C-Falconer/Inscryption/Code/Python/Resources/Images/Background3.jpg

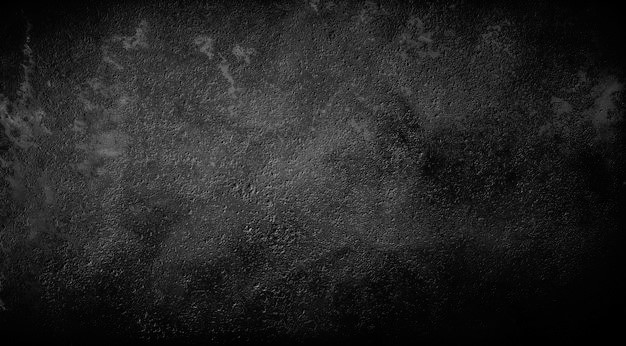
Code/Python/Resources/Images/Background3.jpg
