C-Falconer/Inscryption/Code/Python/Resources/Images/Backgroundv2.3.jpg

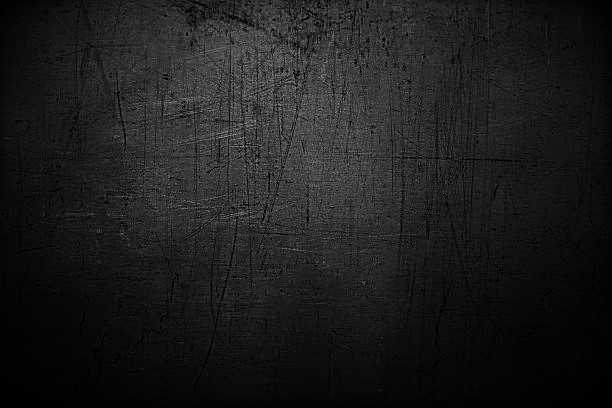
Code/Python/Resources/Images/Backgroundv2.3.jpg
