C-Falconer/Inscryption/Code/Python/Resources/Images/CardFront.png

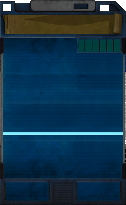
Code/Python/Resources/Images/CardFront.png
