C-Falconer/Inscryption/Code/Python/Resources/Images/Cards/49er.png

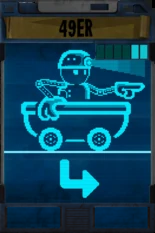
Code/Python/Resources/Images/Cards/49er.png
