C-Falconer/Inscryption/Code/Python/Resources/Images/Cards/Alarm_Bot.png

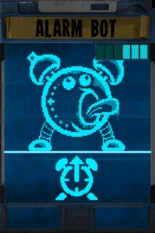
Code/Python/Resources/Images/Cards/Alarm_Bot.png
