C-Falconer/Inscryption/Code/Python/Resources/Images/Cards/Amoebot.png

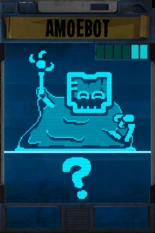
Code/Python/Resources/Images/Cards/Amoebot.png
