C-Falconer/Inscryption/Code/Python/Resources/Images/Cards/Automaton.png

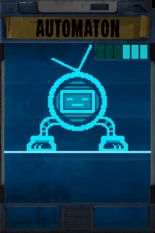
Code/Python/Resources/Images/Cards/Automaton.png
