C-Falconer/Inscryption/Code/Python/Resources/Images/Cards/Bad_Fish.png

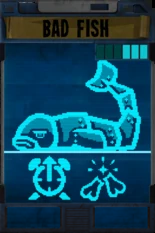
Code/Python/Resources/Images/Cards/Bad_Fish.png
