C-Falconer/Inscryption/Code/Python/Resources/Images/Cards/Bleenes_Vessel.png

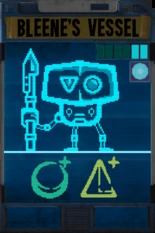
Code/Python/Resources/Images/Cards/Bleenes_Vessel.png
