C-Falconer/Inscryption/Code/Python/Resources/Images/Cards/Bolthound.png

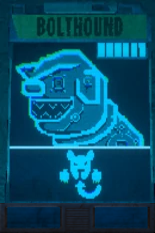
Code/Python/Resources/Images/Cards/Bolthound.png
