C-Falconer/Inscryption/Code/Python/Resources/Images/Cards/Bomb_Latcher.png

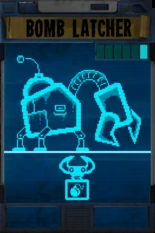
Code/Python/Resources/Images/Cards/Bomb_Latcher.png
