C-Falconer/Inscryption/Code/Python/Resources/Images/Cards/Buff_Conduit.png

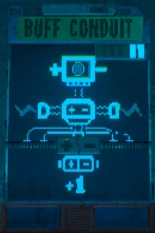
Code/Python/Resources/Images/Cards/Buff_Conduit.png
