C-Falconer/Inscryption/Code/Python/Resources/Images/Cards/Double_Gunner.png

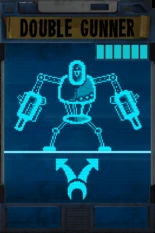
Code/Python/Resources/Images/Cards/Double_Gunner.png
