C-Falconer/Inscryption/Code/Python/Resources/Images/Cards/Emerald_Vessel.png

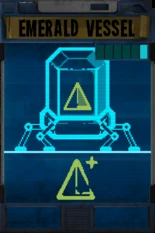
Code/Python/Resources/Images/Cards/Emerald_Vessel.png
