C-Falconer/Inscryption/Code/Python/Resources/Images/Cards/Empty_Vessel.png

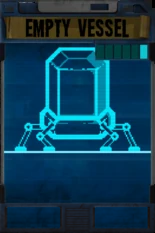
Code/Python/Resources/Images/Cards/Empty_Vessel.png
