C-Falconer/Inscryption/Code/Python/Resources/Images/Cards/Energy_Bot.png

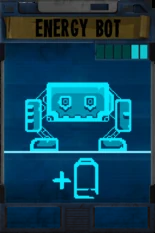
Code/Python/Resources/Images/Cards/Energy_Bot.png
