C-Falconer/Inscryption/Code/Python/Resources/Images/Cards/Exeskeleton.png

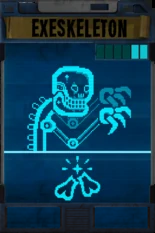
Code/Python/Resources/Images/Cards/Exeskeleton.png
