C-Falconer/Inscryption/Code/Python/Resources/Images/Cards/Explode_Bot.png

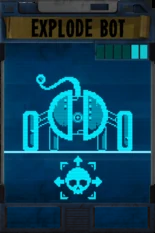
Code/Python/Resources/Images/Cards/Explode_Bot.png
