C-Falconer/Inscryption/Code/Python/Resources/Images/Cards/Gem_Detonator.png

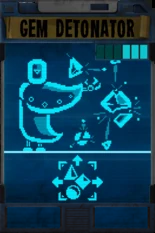
Code/Python/Resources/Images/Cards/Gem_Detonator.png
