C-Falconer/Inscryption/Code/Python/Resources/Images/Cards/Gem_Guardian.png

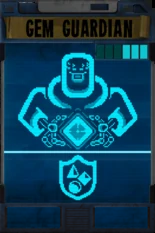
Code/Python/Resources/Images/Cards/Gem_Guardian.png
