C-Falconer/Inscryption/Code/Python/Resources/Images/Cards/Gembound_Ripper.png

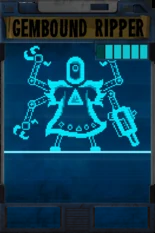
Code/Python/Resources/Images/Cards/Gembound_Ripper.png
