C-Falconer/Inscryption/Code/Python/Resources/Images/Cards/Gems_Conduit.png

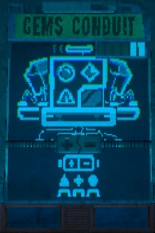
Code/Python/Resources/Images/Cards/Gems_Conduit.png
