C-Falconer/Inscryption/Code/Python/Resources/Images/Cards/Good_Fish.png

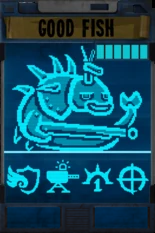
Code/Python/Resources/Images/Cards/Good_Fish.png
