C-Falconer/Inscryption/Code/Python/Resources/Images/Cards/Goranjs_Vessel.png

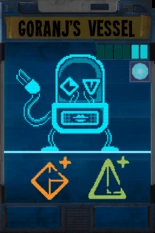
Code/Python/Resources/Images/Cards/Goranjs_Vessel.png
