C-Falconer/Inscryption/Code/Python/Resources/Images/Cards/Gr1z_T.png

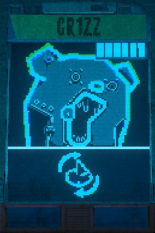
Code/Python/Resources/Images/Cards/Gr1z_T.png
