C-Falconer/Inscryption/Code/Python/Resources/Images/Cards/GR1ZZ.png

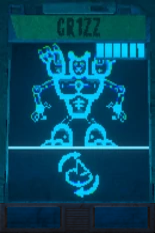
Code/Python/Resources/Images/Cards/GR1ZZ.png
