C-Falconer/Inscryption/Code/Python/Resources/Images/Cards/GR1ZZ_T.png

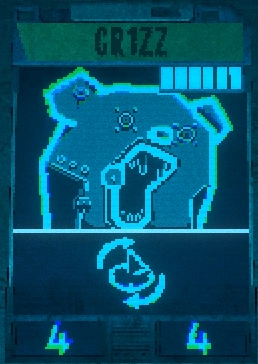
Code/Python/Resources/Images/Cards/GR1ZZ_T.png
