C-Falconer/Inscryption/Code/Python/Resources/Images/Cards/Insectodrone.png

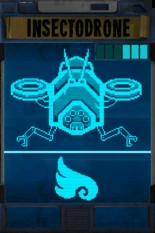
Code/Python/Resources/Images/Cards/Insectodrone.png
