C-Falconer/Inscryption/Code/Python/Resources/Images/Cards/Kind_Cell.png

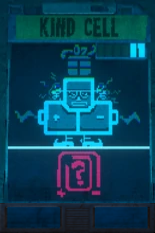
Code/Python/Resources/Images/Cards/Kind_Cell.png
