C-Falconer/Inscryption/Code/Python/Resources/Images/Cards/L33pbot.png

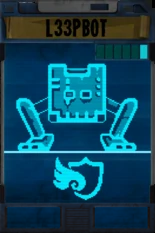
Code/Python/Resources/Images/Cards/L33pbot.png
