C-Falconer/Inscryption/Code/Python/Resources/Images/Cards/Lonely_Wizbot.png

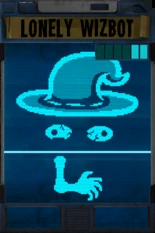
Code/Python/Resources/Images/Cards/Lonely_Wizbot.png
