C-Falconer/Inscryption/Code/Python/Resources/Images/Cards/More_Fish.png

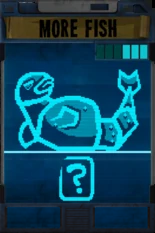
Code/Python/Resources/Images/Cards/More_Fish.png
