C-Falconer/Inscryption/Code/Python/Resources/Images/Cards/Null_Conduit.png

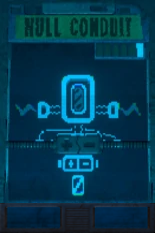
Code/Python/Resources/Images/Cards/Null_Conduit.png
