C-Falconer/Inscryption/Code/Python/Resources/Images/Cards/Orlus_Vessel.png

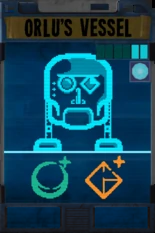
Code/Python/Resources/Images/Cards/Orlus_Vessel.png
