C-Falconer/Inscryption/Code/Python/Resources/Images/Cards/Qu17_T.png

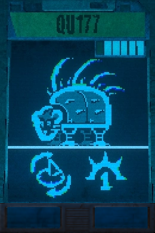
Code/Python/Resources/Images/Cards/Qu17_T.png
