C-Falconer/Inscryption/Code/Python/Resources/Images/Cards/Ruby_Vessel.png

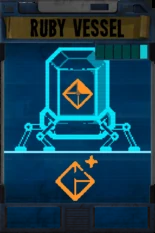
Code/Python/Resources/Images/Cards/Ruby_Vessel.png
