C-Falconer/Inscryption/Code/Python/Resources/Images/Cards/Sapphire_Vessel.png

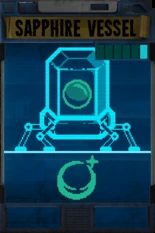
Code/Python/Resources/Images/Cards/Sapphire_Vessel.png
