C-Falconer/Inscryption/Code/Python/Resources/Images/Cards/Shield_Latcher.png

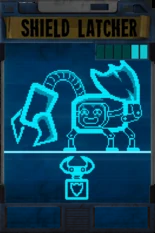
Code/Python/Resources/Images/Cards/Shield_Latcher.png
