C-Falconer/Inscryption/Code/Python/Resources/Images/Cards/Shieldbot.png

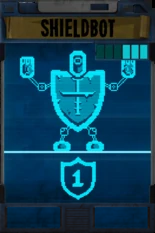
Code/Python/Resources/Images/Cards/Shieldbot.png
