C-Falconer/Inscryption/Code/Python/Resources/Images/Cards/Skel-E-Latcher.png

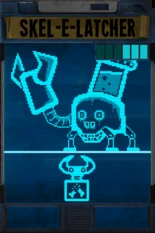
Code/Python/Resources/Images/Cards/Skel-E-Latcher.png
