C-Falconer/Inscryption/Code/Python/Resources/Images/Cards/Son1_T.png

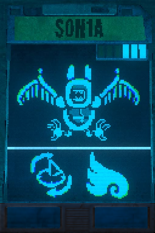
Code/Python/Resources/Images/Cards/Son1_T.png
