C-Falconer/Inscryption/Code/Python/Resources/Images/Cards/SON1A.png

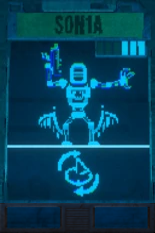
Code/Python/Resources/Images/Cards/SON1A.png
