C-Falconer/Inscryption/Code/Python/Resources/Images/Cards/SON1A_T.png

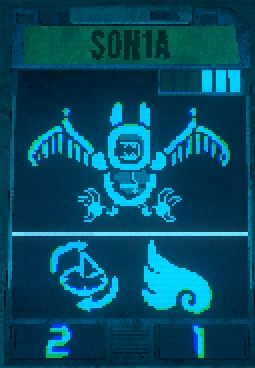
Code/Python/Resources/Images/Cards/SON1A_T.png
