C-Falconer/Inscryption/Code/Python/Resources/Images/Cards/Splinter_Cell.png

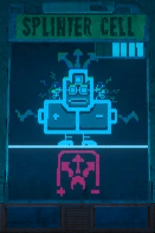
Code/Python/Resources/Images/Cards/Splinter_Cell.png
