C-Falconer/Inscryption/Code/Python/Resources/Images/Cards/Swapbot.png

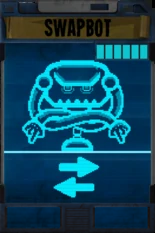
Code/Python/Resources/Images/Cards/Swapbot.png
