C-Falconer/Inscryption/Code/Python/Resources/Images/Cards/Tough_Cell.png

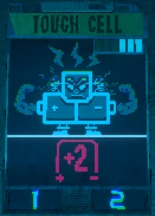
Code/Python/Resources/Images/Cards/Tough_Cell.png
