C-Falconer/Inscryption/Code/Python/Resources/Images/Cards/ZZZ.png

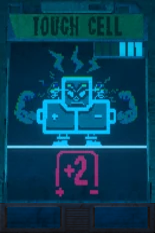
Code/Python/Resources/Images/Cards/ZZZ.png
