C-Falconer/Inscryption/Code/Python/Resources/Images/CardSlot.png

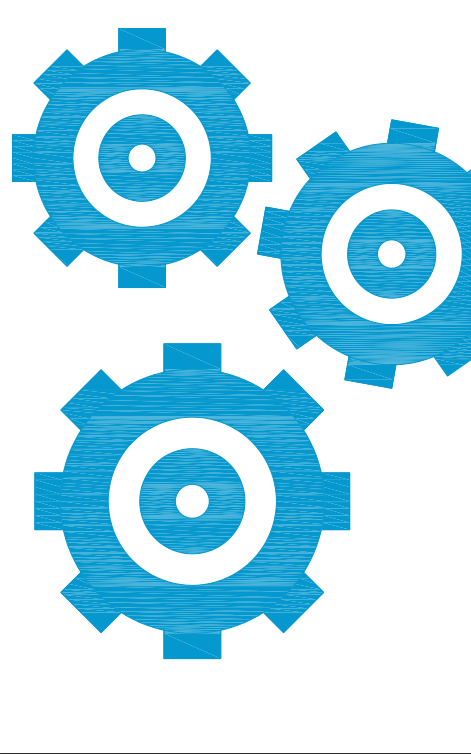
Code/Python/Resources/Images/CardSlot.png
