C-Falconer/Inscryption/Fritzing/Inscryption.png

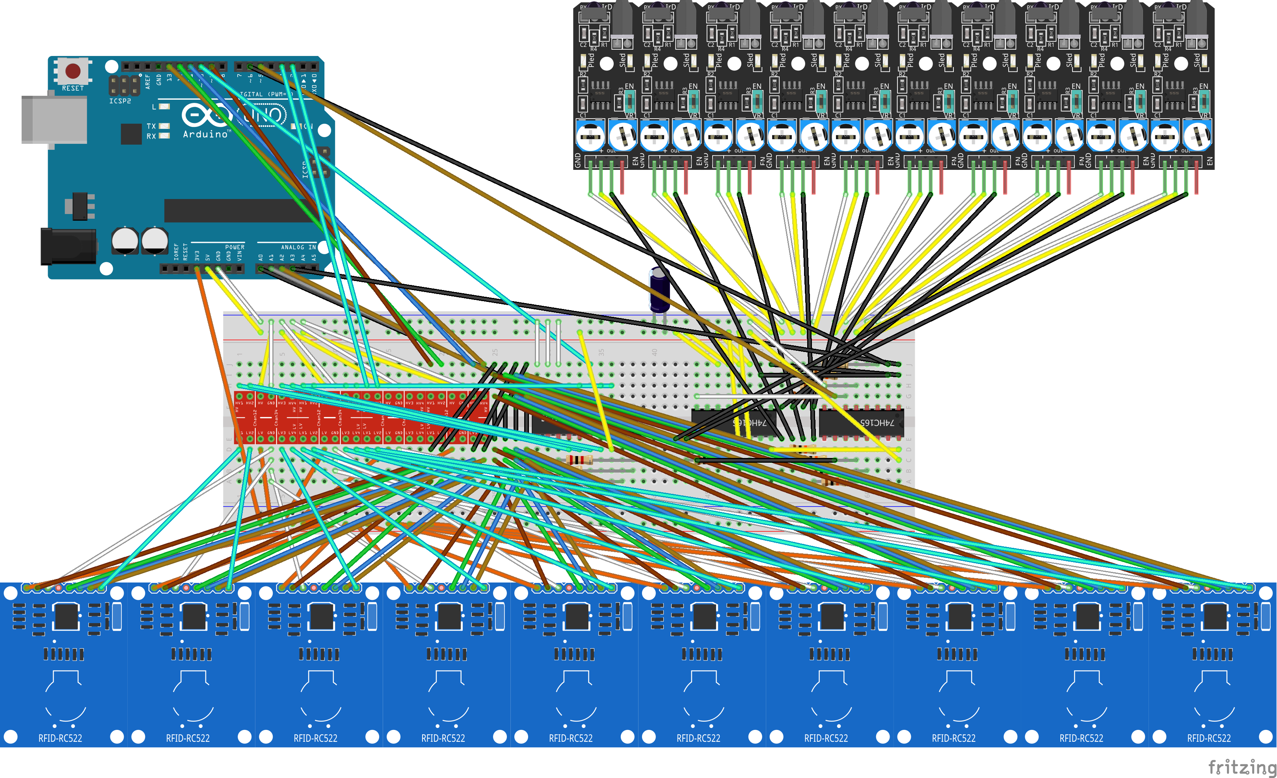
Fritzing/Inscryption.png
