C-Falconer/Inscryption/Project_Journey_Files/20220519_193213.jpg

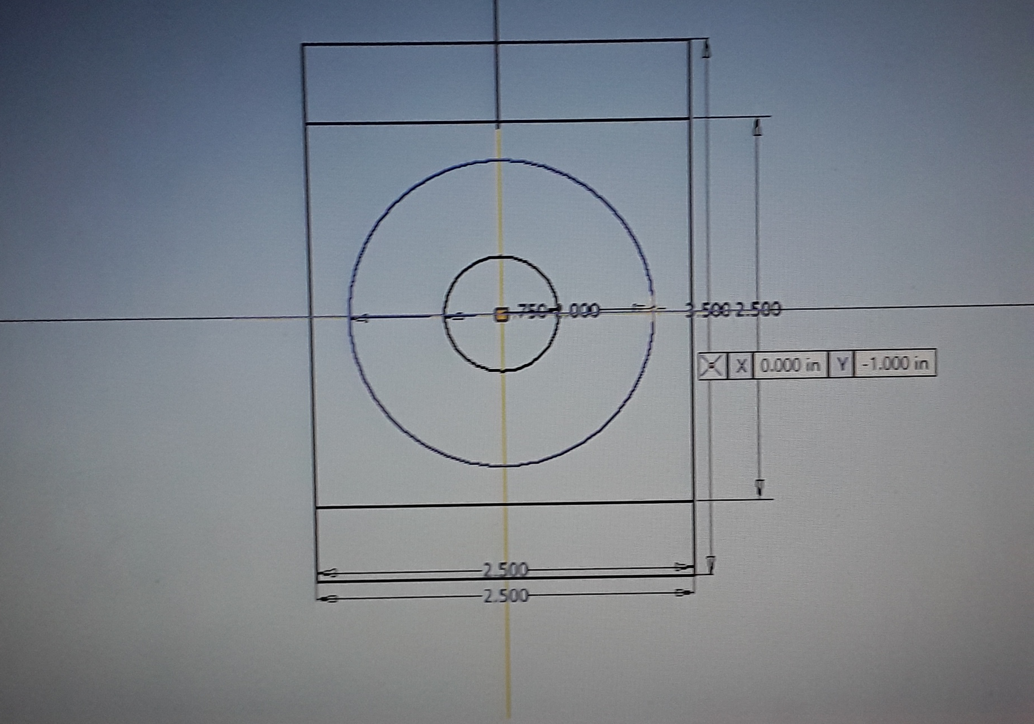
Project_Journey_Files/20220519_193213.jpg
