C-Falconer/Inscryption/Project_Journey_Files/20220519_201609.jpg

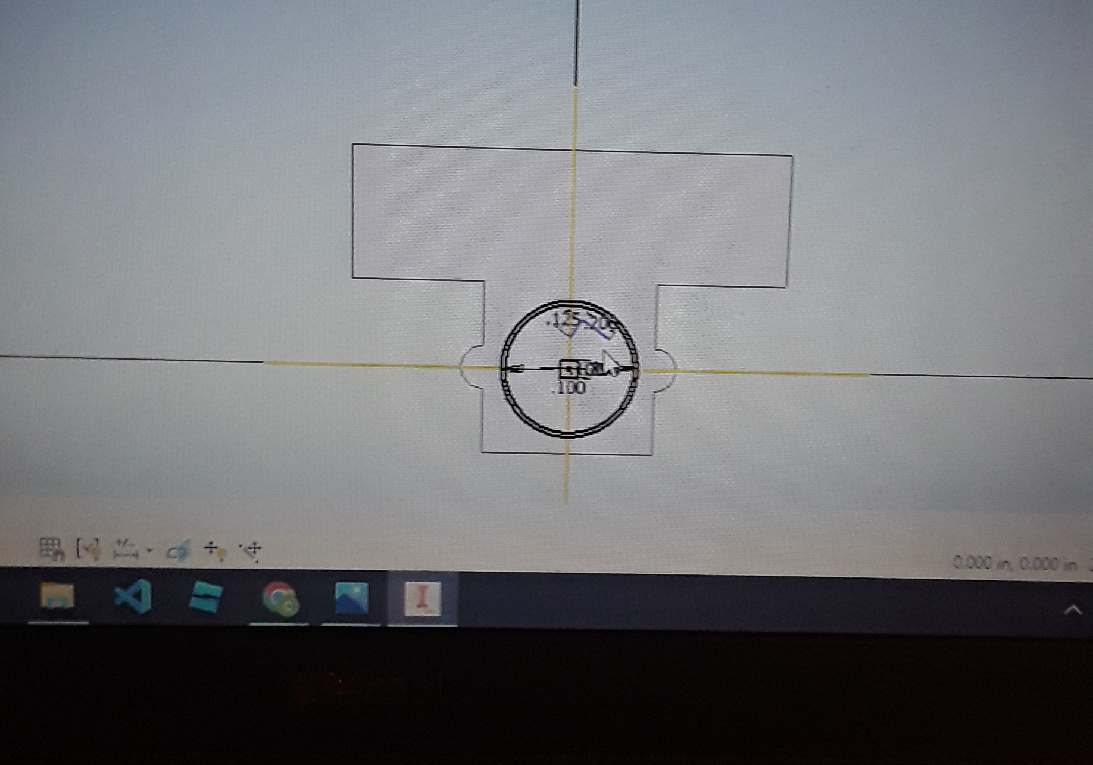
Project_Journey_Files/20220519_201609.jpg
