C-Falconer/Inscryption/Project_Journey_Files/20220519_205204.jpg

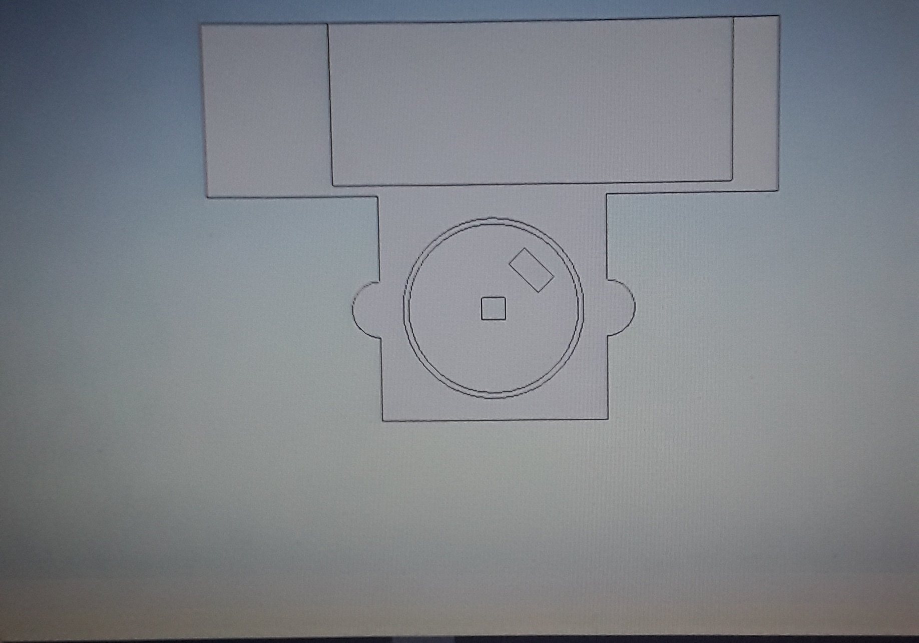
Project_Journey_Files/20220519_205204.jpg
