C-Falconer/Inscryption/Project_Journey_Files/20220520_001646.jpg

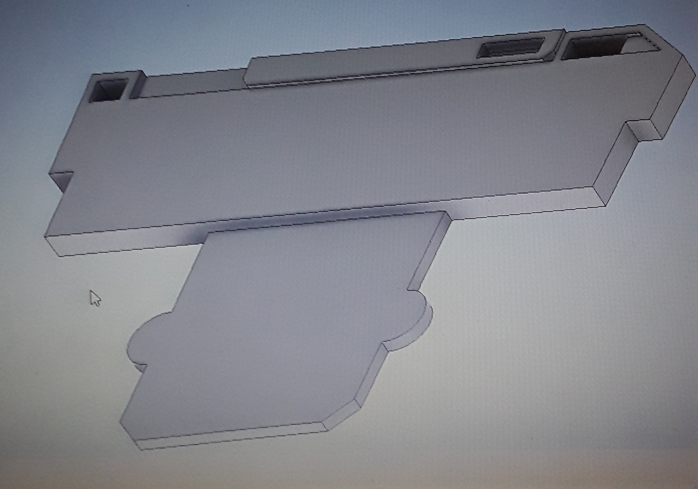
Project_Journey_Files/20220520_001646.jpg
