C-Falconer/Inscryption/Project_Journey_Files/20220520_161351.jpg

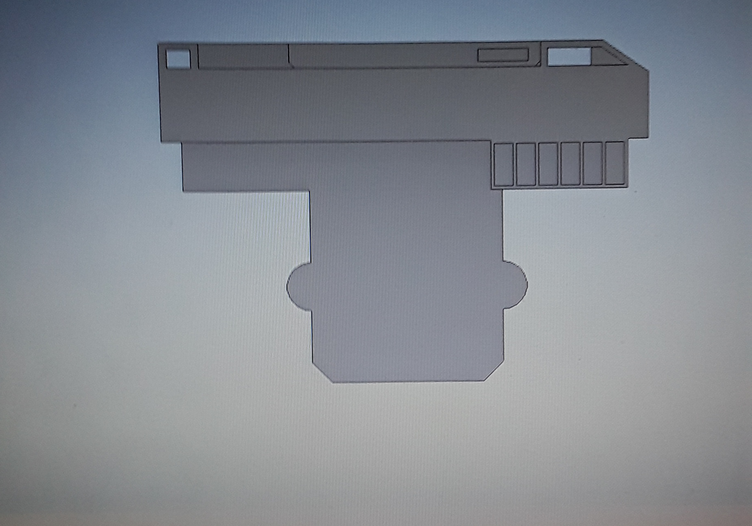
Project_Journey_Files/20220520_161351.jpg
