C-Falconer/Inscryption/Project_Journey_Files/20220526_223827.jpg

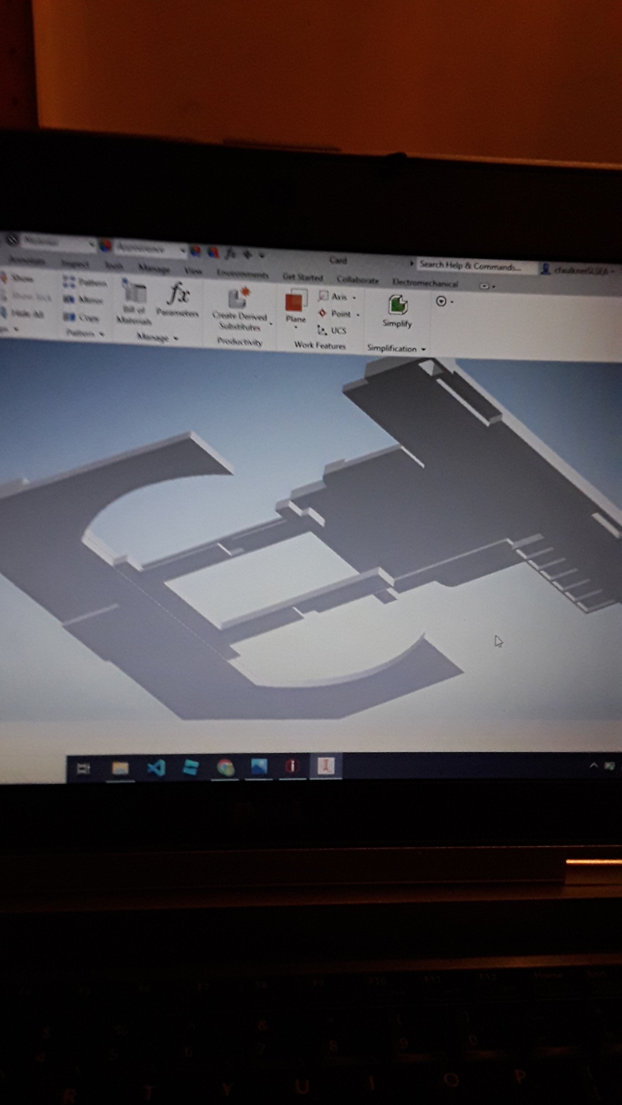
Project_Journey_Files/20220526_223827.jpg
