C-Falconer/Inscryption/Project_Journey_Files/20220526_224056.jpg

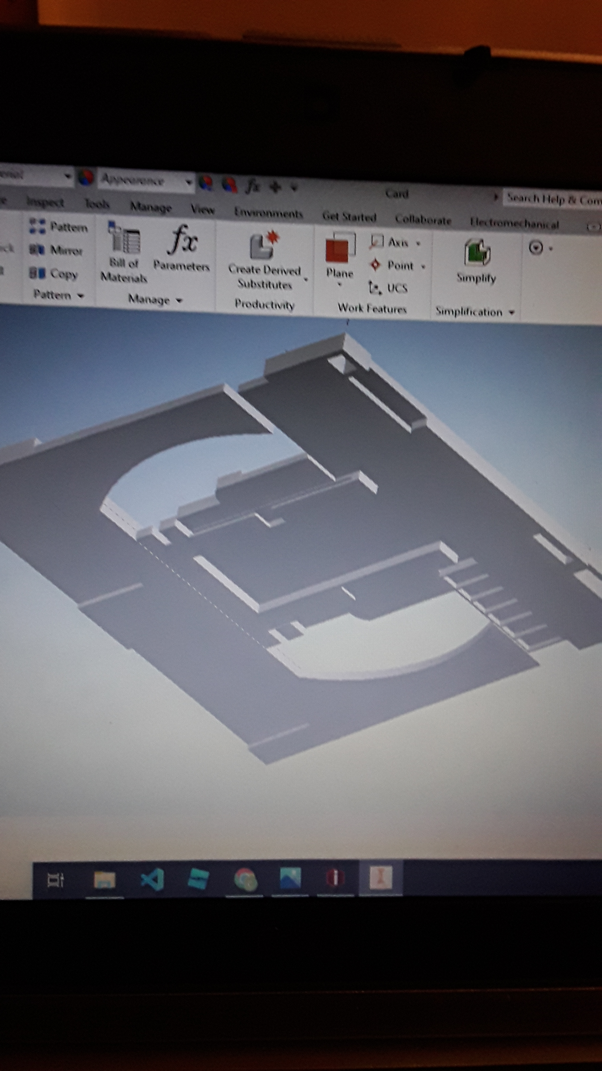
Project_Journey_Files/20220526_224056.jpg
