C-Falconer/Inscryption/Project_Journey_Files/20220602_181350.jpg

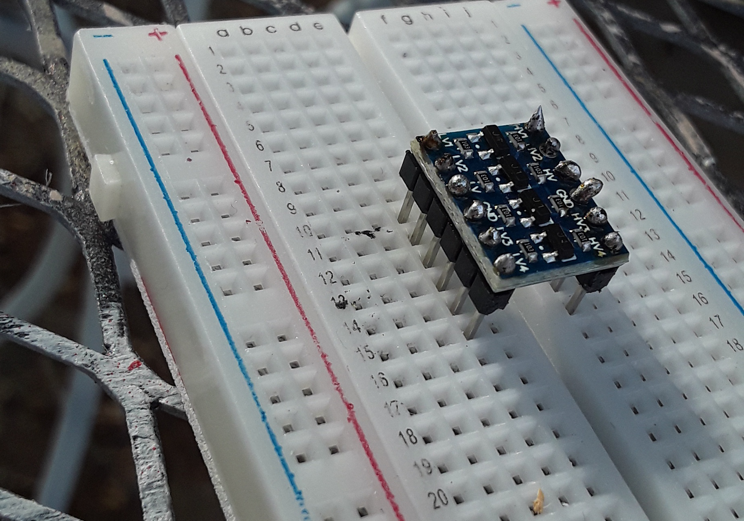
Project_Journey_Files/20220602_181350.jpg
