C-Falconer/Inscryption/Project_Journey_Files/20220630_130943.jpg

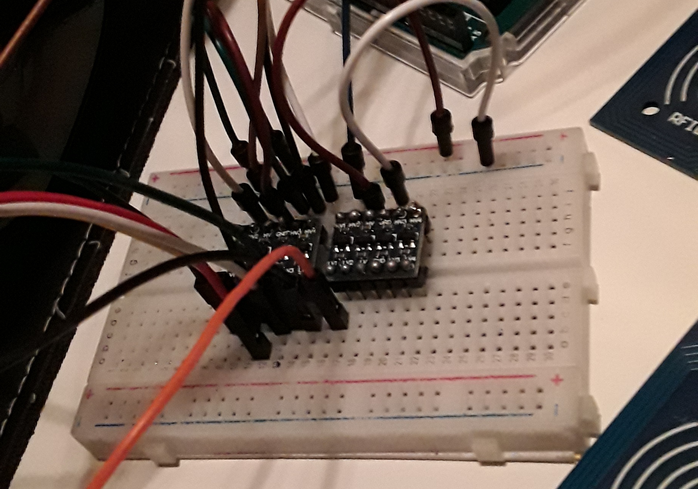
Project_Journey_Files/20220630_130943.jpg
