C-Falconer/Inscryption/Project_Journey_Files/20220630_142103.jpg

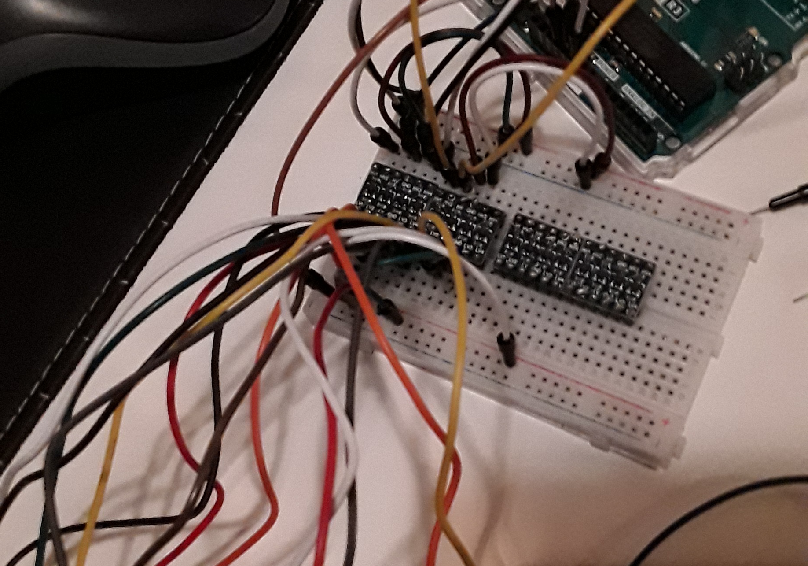
Project_Journey_Files/20220630_142103.jpg
