C-Falconer/Inscryption/Project_Journey_Files/20220701_140546.jpg

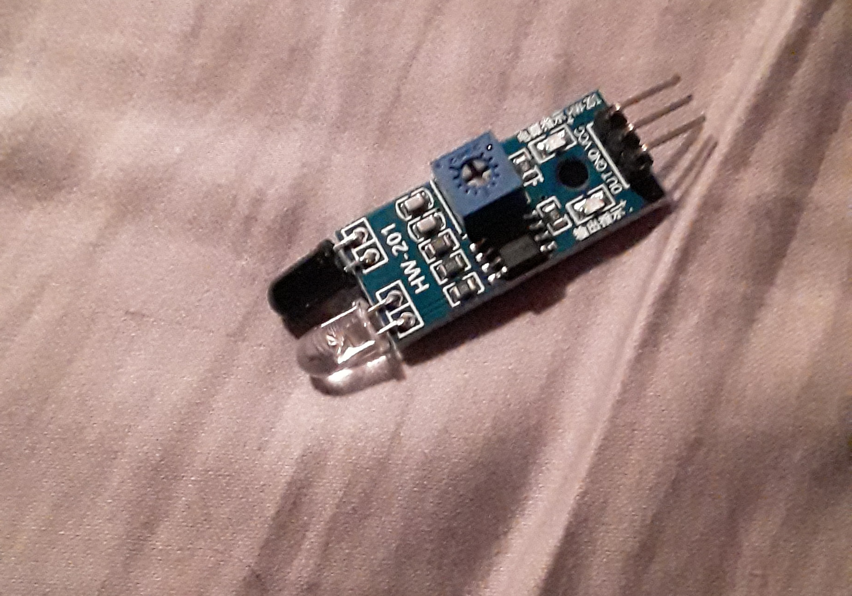
Project_Journey_Files/20220701_140546.jpg
