C-Falconer/Inscryption/Project_Journey_Files/20220701_145914.jpg

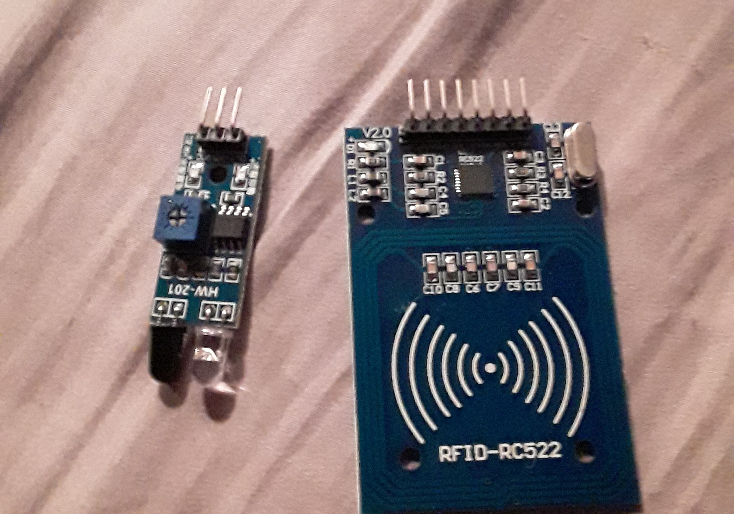
Project_Journey_Files/20220701_145914.jpg
