C-Falconer/Inscryption/Project_Journey_Files/20220701_183045.jpg

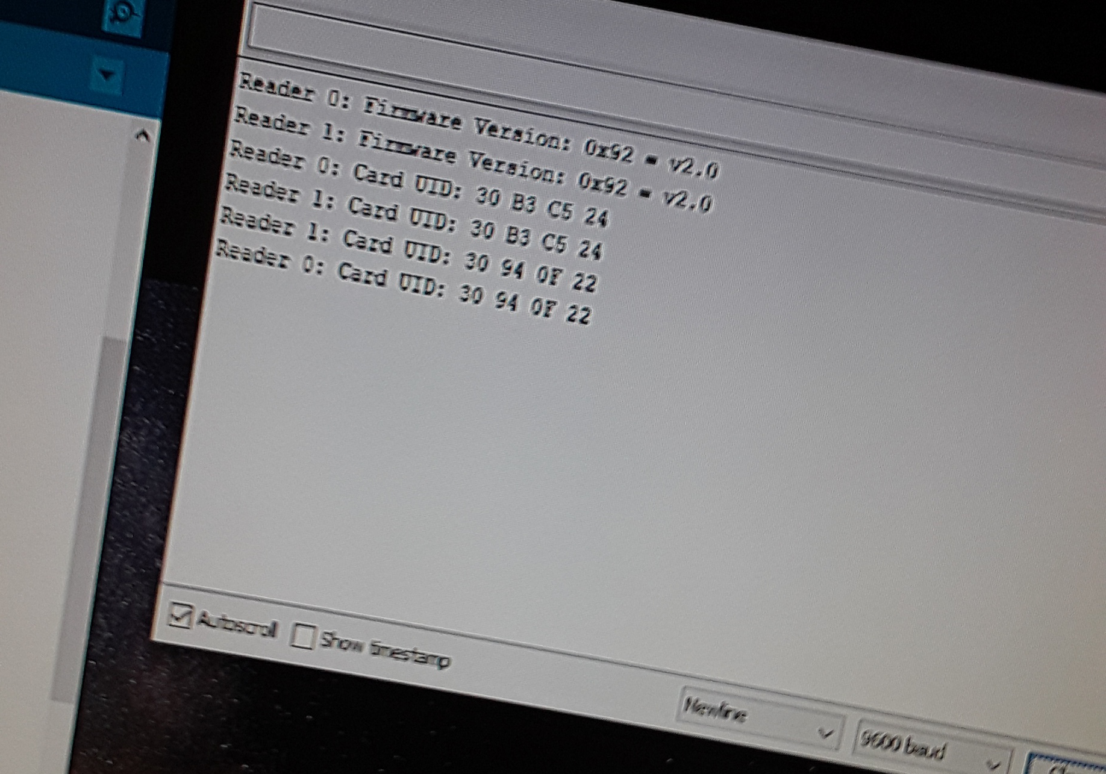
Project_Journey_Files/20220701_183045.jpg
