C-Falconer/Inscryption/Project_Journey_Files/20220701_183055.jpg

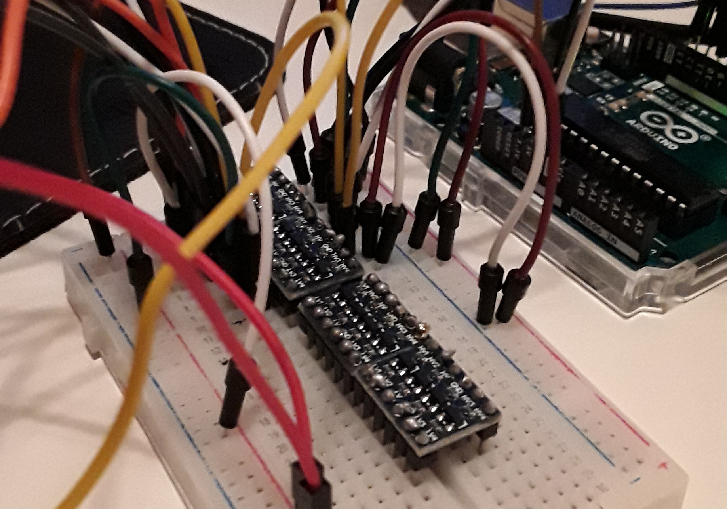
Project_Journey_Files/20220701_183055.jpg
