C-Falconer/Inscryption/Project_Journey_Files/20220704_204045.jpg

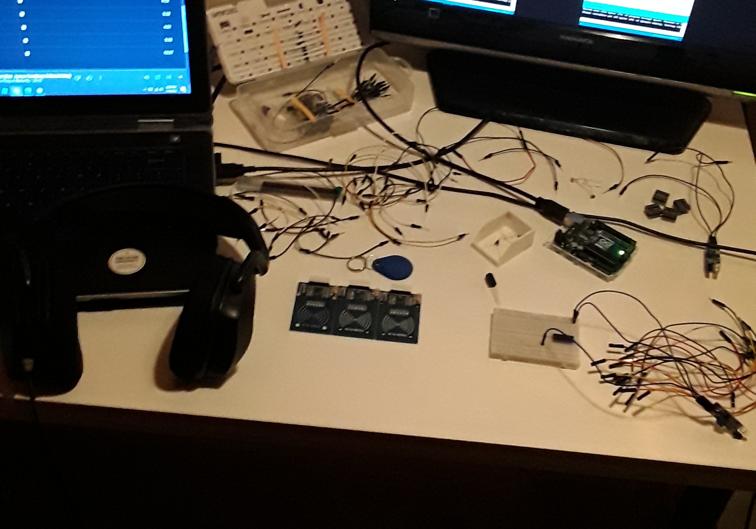
Project_Journey_Files/20220704_204045.jpg
