C-Falconer/Inscryption/Project_Journey_Files/20220704_210424.jpg

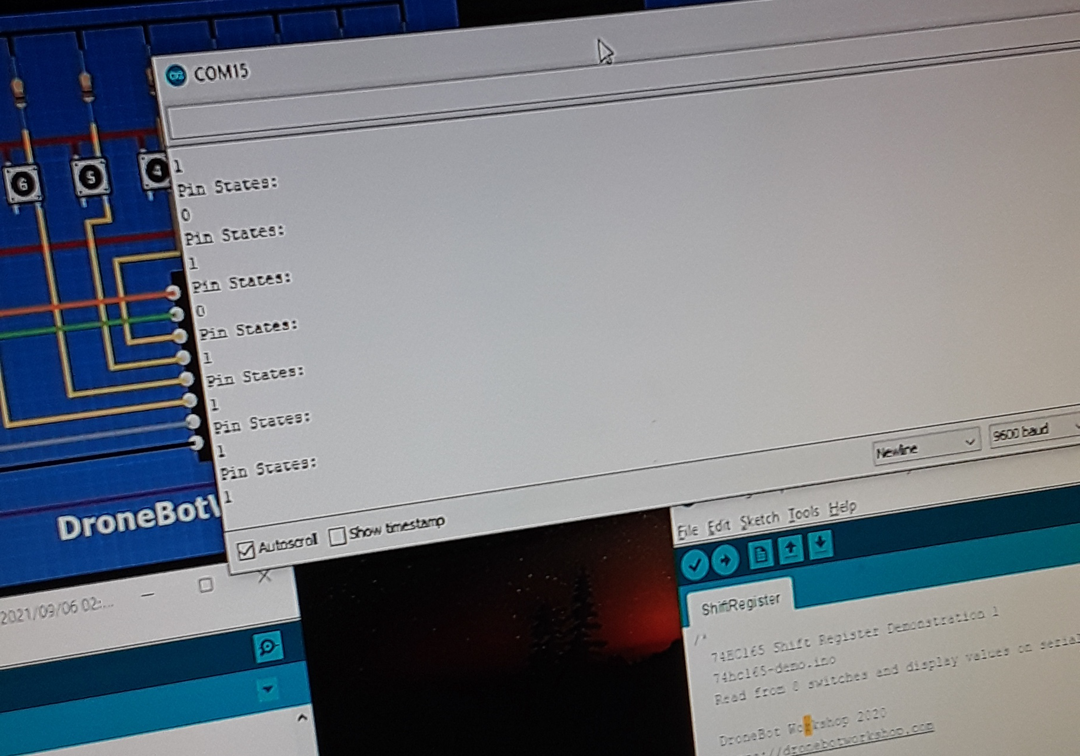
Project_Journey_Files/20220704_210424.jpg
