C-Falconer/Inscryption/Project_Journey_Files/20220704_212249.jpg

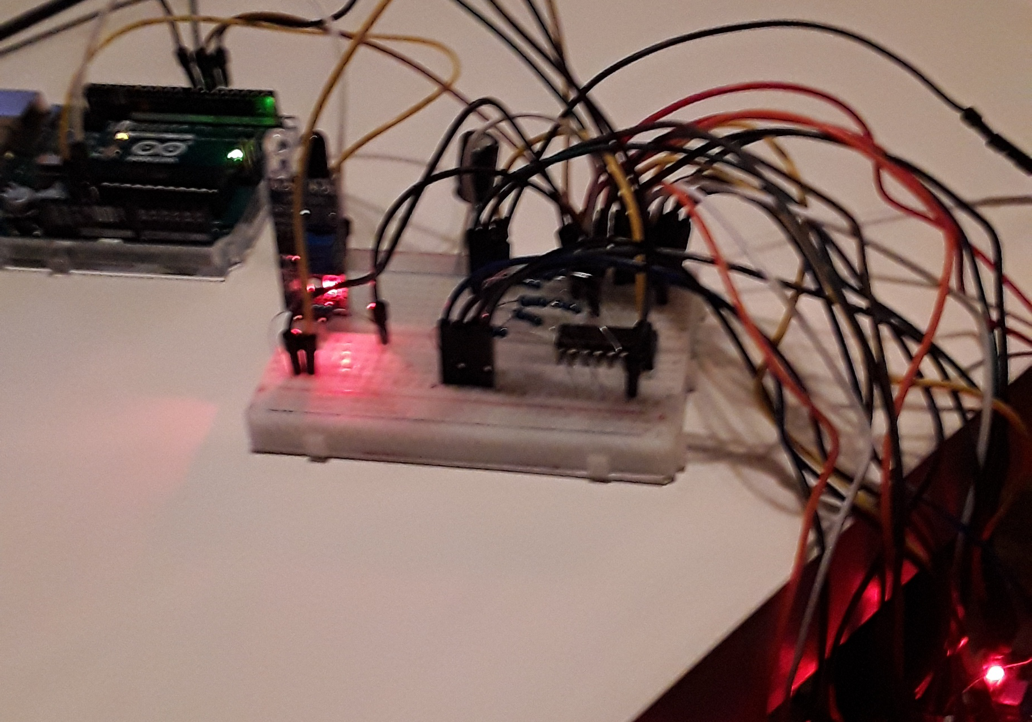
Project_Journey_Files/20220704_212249.jpg
