C-Falconer/Inscryption/Project_Journey_Files/20220707_152534.jpg

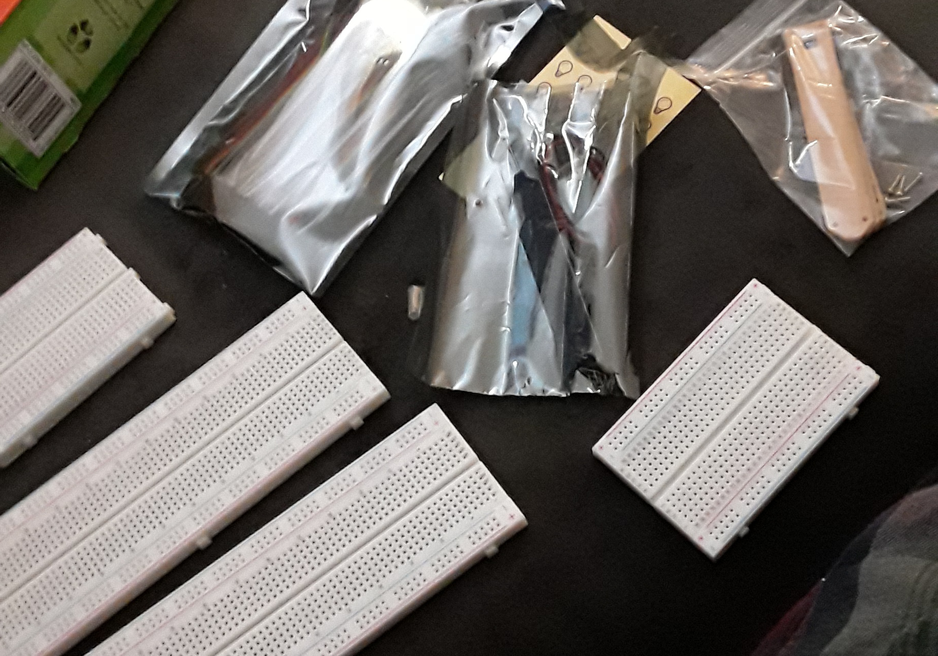
Project_Journey_Files/20220707_152534.jpg
