C-Falconer/Inscryption/Project_Journey_Files/20220707_154334.jpg

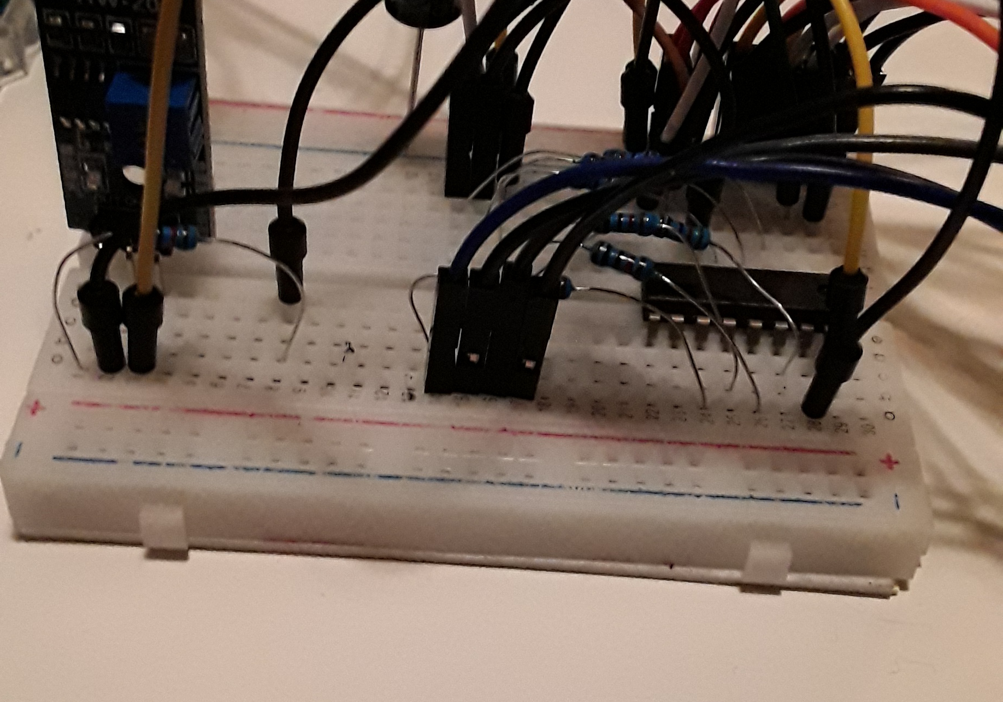
Project_Journey_Files/20220707_154334.jpg
