C-Falconer/Inscryption/Project_Journey_Files/20220707_164636.jpg

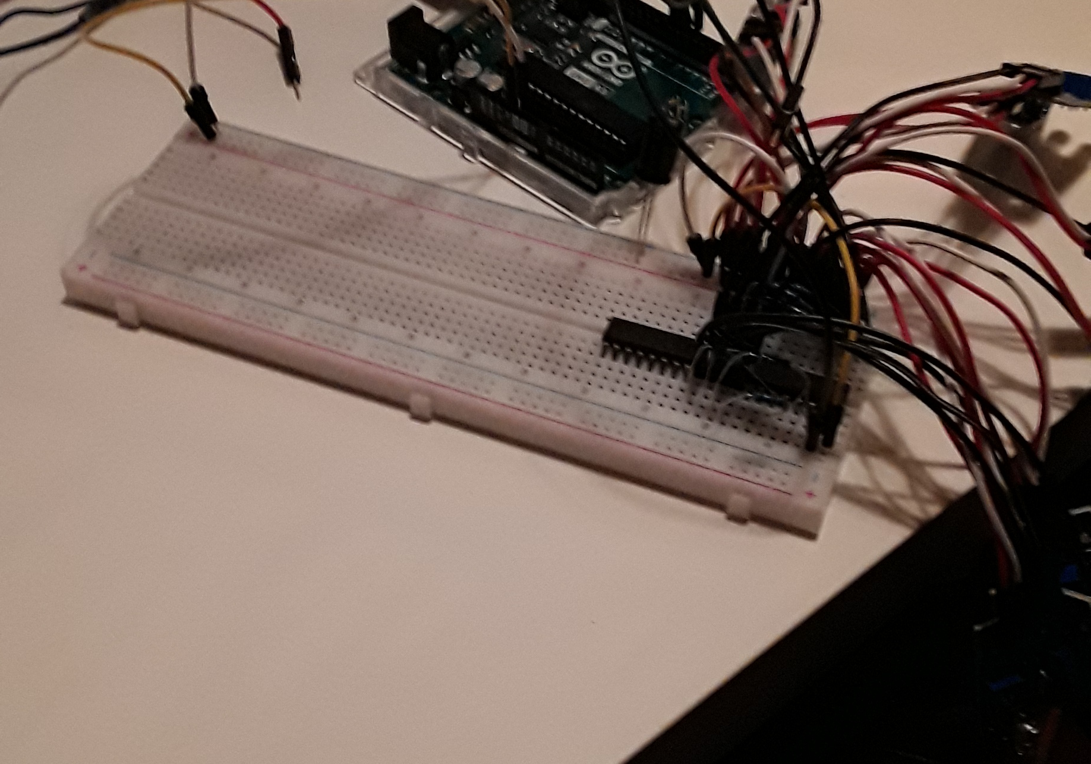
Project_Journey_Files/20220707_164636.jpg
