C-Falconer/Inscryption/Project_Journey_Files/20220707_164910.jpg

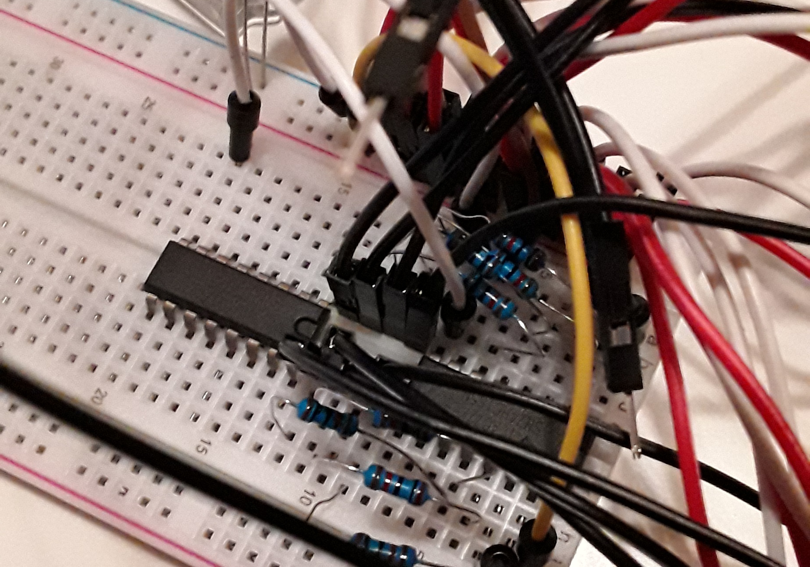
Project_Journey_Files/20220707_164910.jpg
