C-Falconer/Inscryption/Project_Journey_Files/20220707_170357.jpg

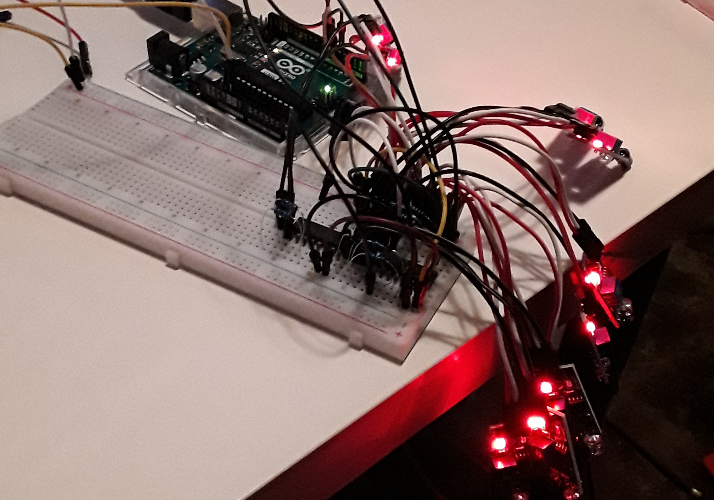
Project_Journey_Files/20220707_170357.jpg
