C-Falconer/Inscryption/Project_Journey_Files/20220707_171751.jpg

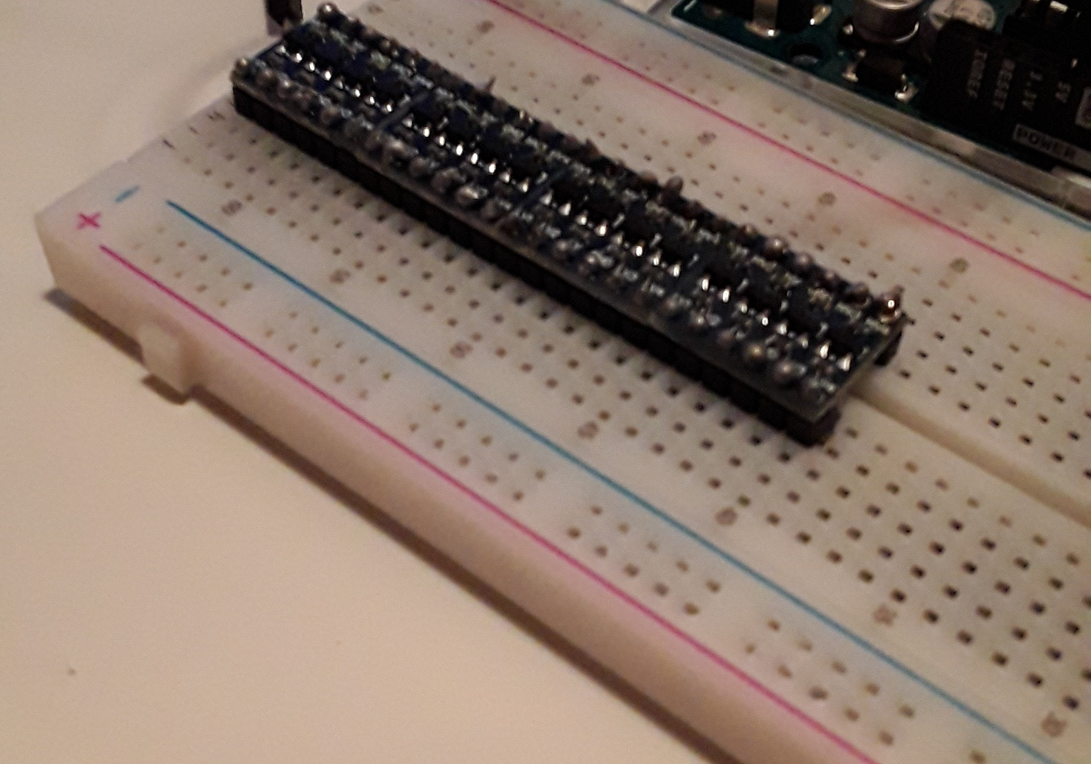
Project_Journey_Files/20220707_171751.jpg
