C-Falconer/Inscryption/Project_Journey_Files/20220707_174355.jpg

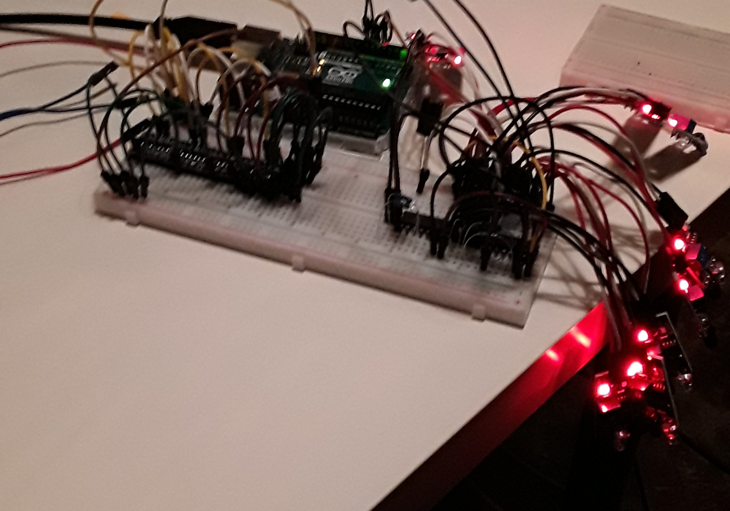
Project_Journey_Files/20220707_174355.jpg
