C-Falconer/Inscryption/Project_Journey_Files/20220714_173739.jpg

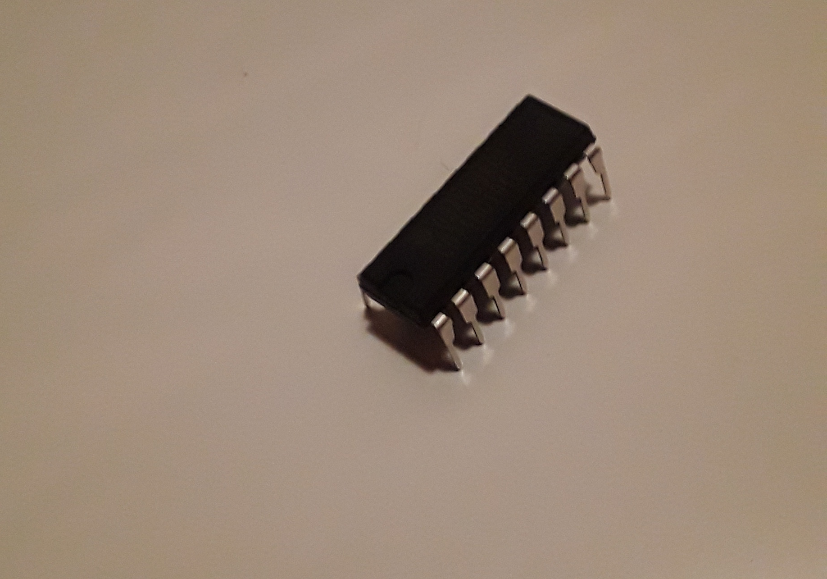
Project_Journey_Files/20220714_173739.jpg
