C-Falconer/Inscryption/Project_Journey_Files/20220721_234322.jpg

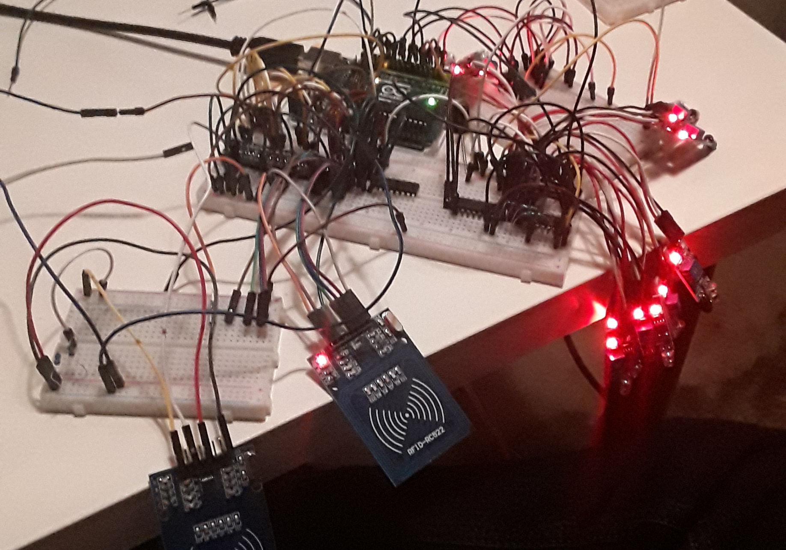
Project_Journey_Files/20220721_234322.jpg
