C-Falconer/Inscryption/Project_Journey_Files/20220801_015247.jpg

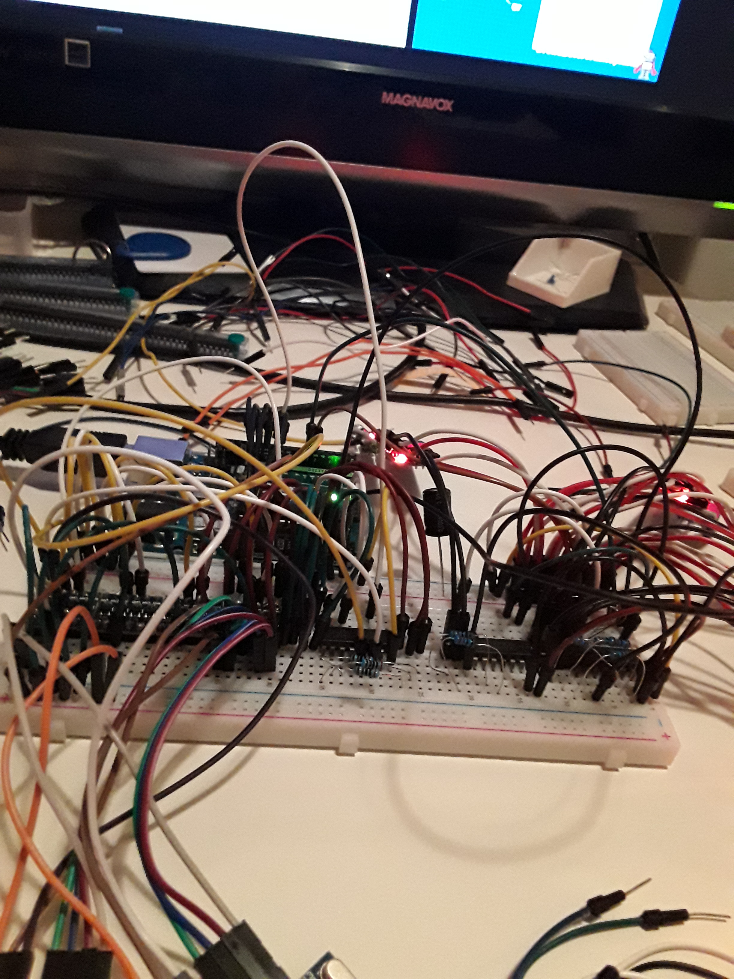
Project_Journey_Files/20220801_015247.jpg
