C-Falconer/Inscryption/Project_Journey_Files/20220801_020231.jpg

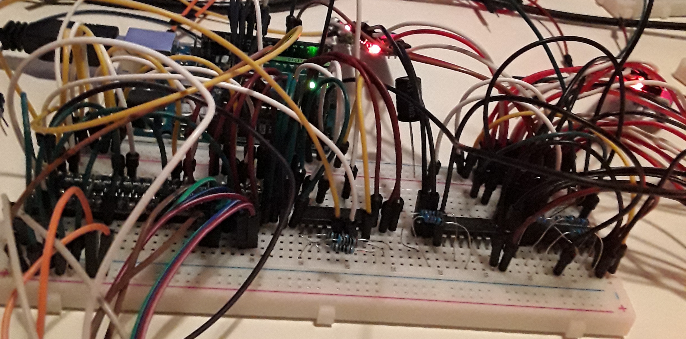
Project_Journey_Files/20220801_020231.jpg
