C-Falconer/Inscryption/Project_Journey_Files/20220802_011312.jpg

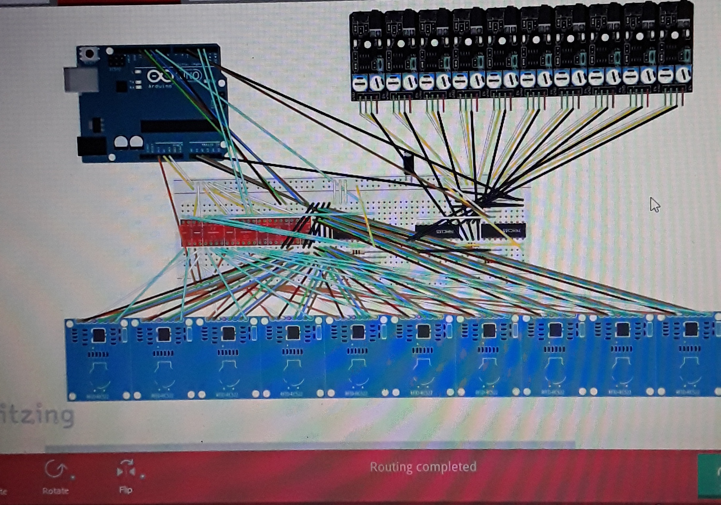
Project_Journey_Files/20220802_011312.jpg
