C-Falconer/Inscryption/Project_Journey_Files/20220802_011532.jpg

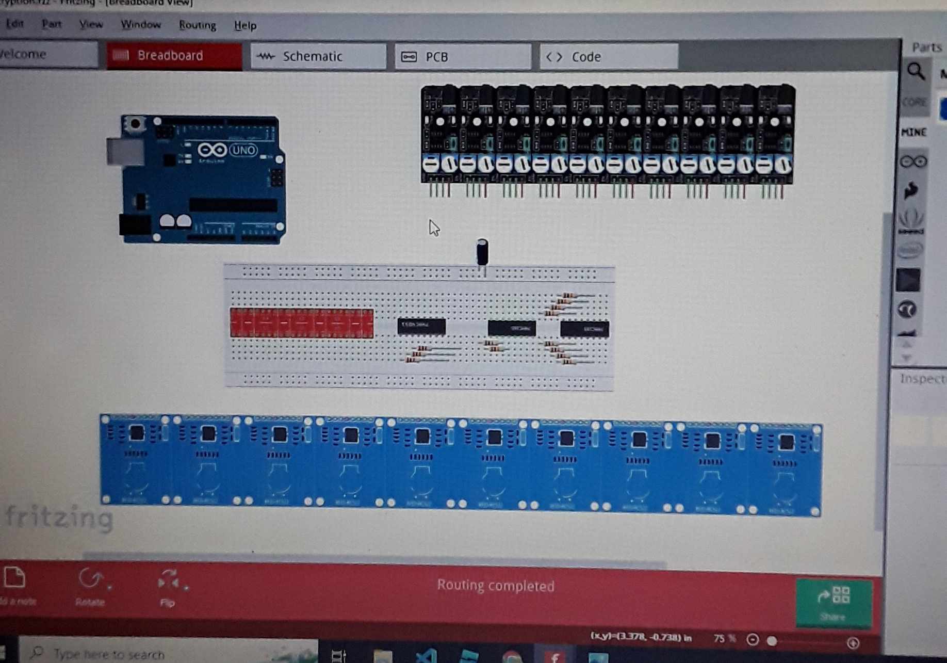
Project_Journey_Files/20220802_011532.jpg
