C-Falconer/Inscryption/Project_Journey_Files/20220802_013706.jpg

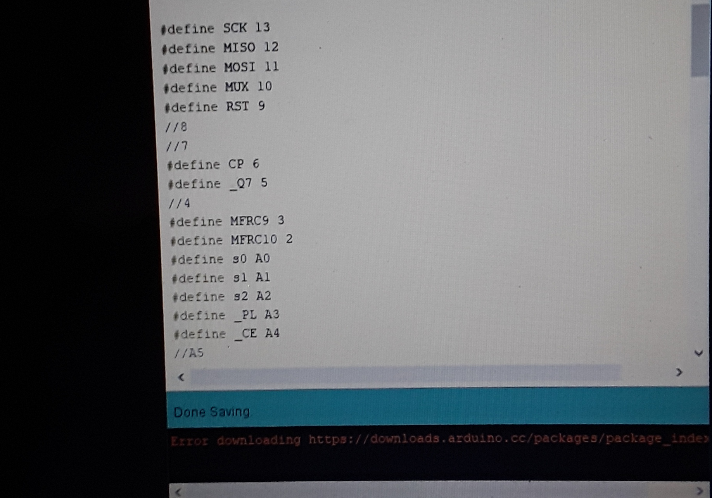
Project_Journey_Files/20220802_013706.jpg
