C-Falconer/Inscryption/Project_Journey_Files/20220807_211640.jpg

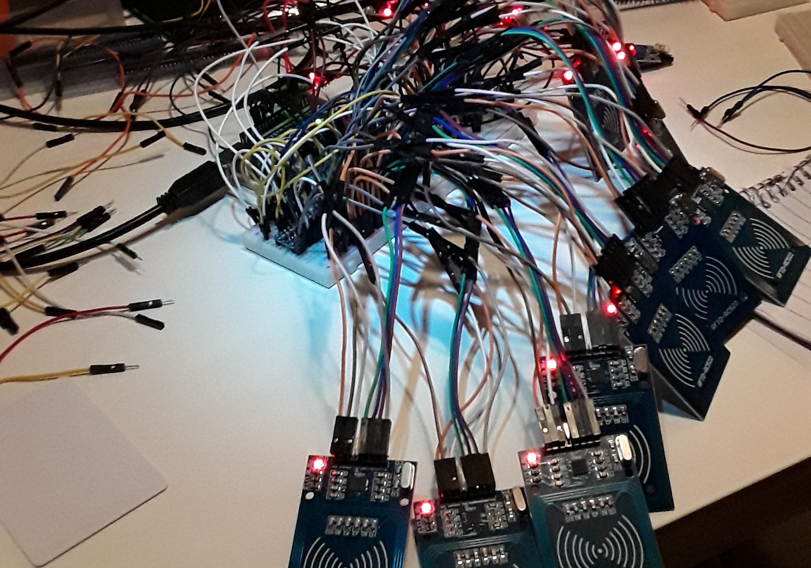
Project_Journey_Files/20220807_211640.jpg
