C-Falconer/Inscryption/Project_Journey_Files/20220810_184311.jpg

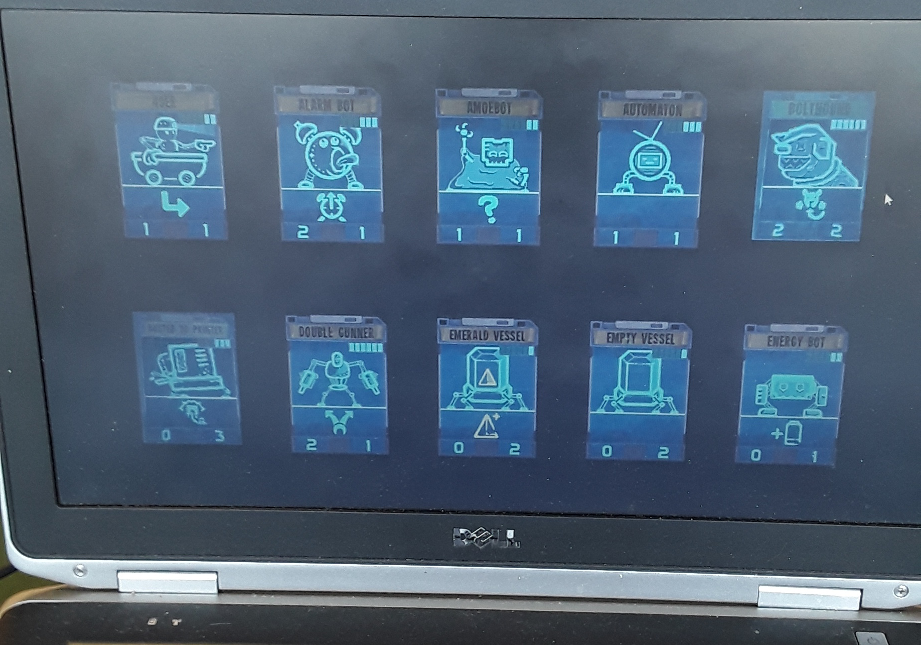
Project_Journey_Files/20220810_184311.jpg
