C-Falconer/Inscryption/Project_Journey_Files/20220811_013951.jpg

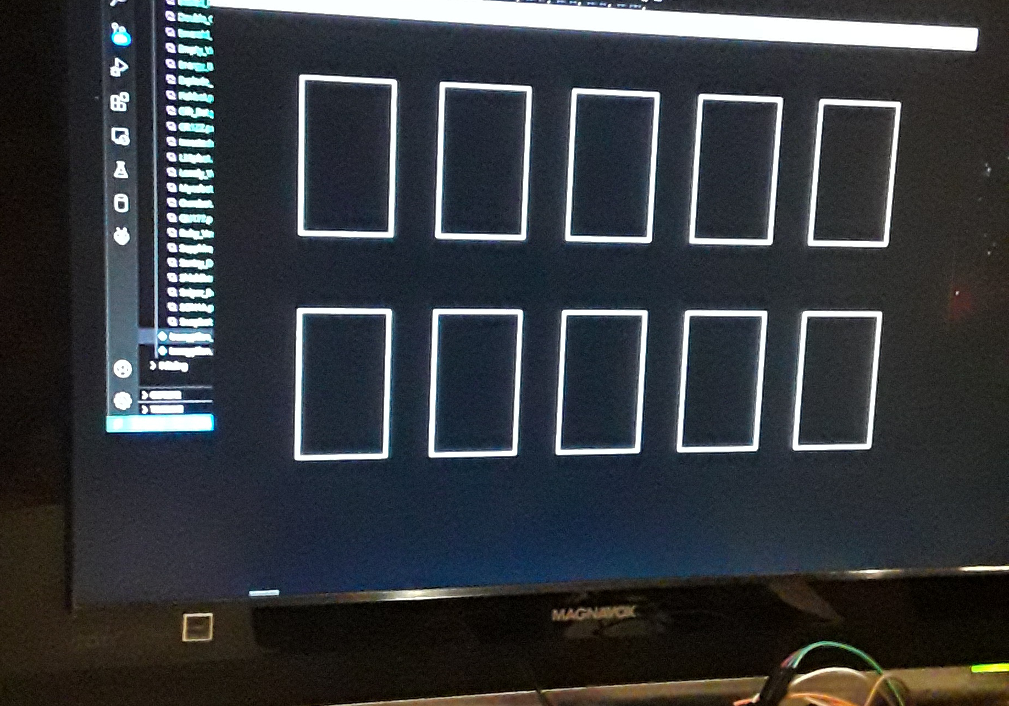
Project_Journey_Files/20220811_013951.jpg
