C-Falconer/Inscryption/Project_Journey_Files/20220811_014026.jpg

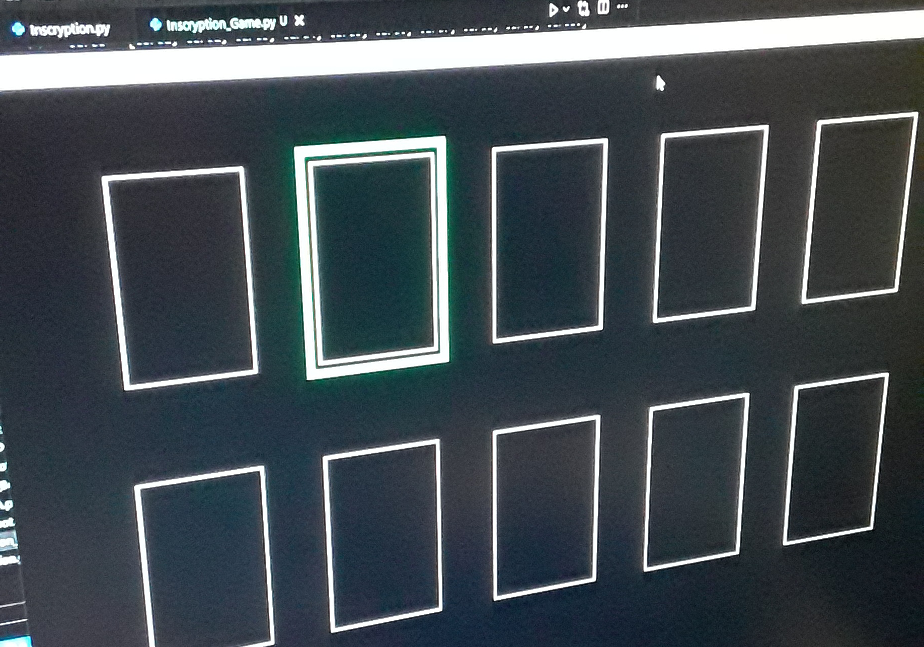
Project_Journey_Files/20220811_014026.jpg
