C-Falconer/Inscryption/Project_Journey_Files/20220811_014100.jpg

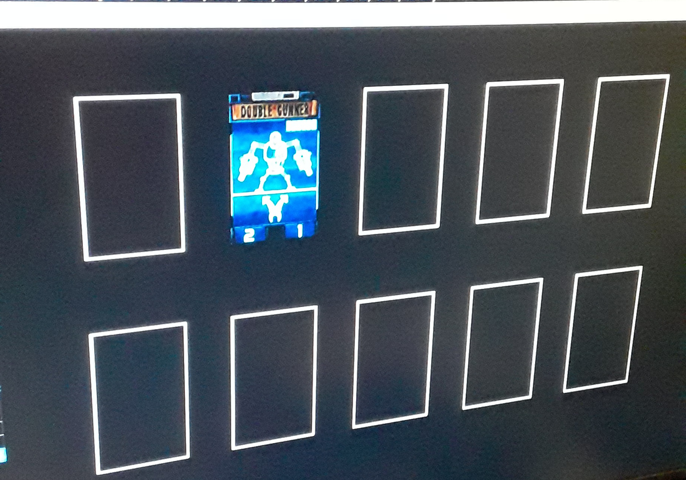
Project_Journey_Files/20220811_014100.jpg
