C-Falconer/Inscryption/Project_Journey_Files/20220812_222904.jpg

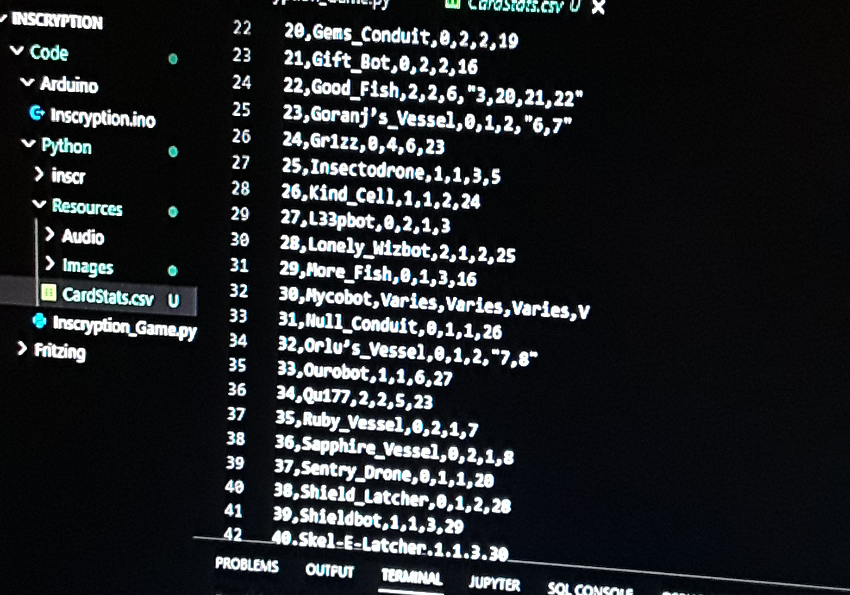
Project_Journey_Files/20220812_222904.jpg
