C-Falconer/Inscryption/Project_Journey_Files/20220815_222312.jpg

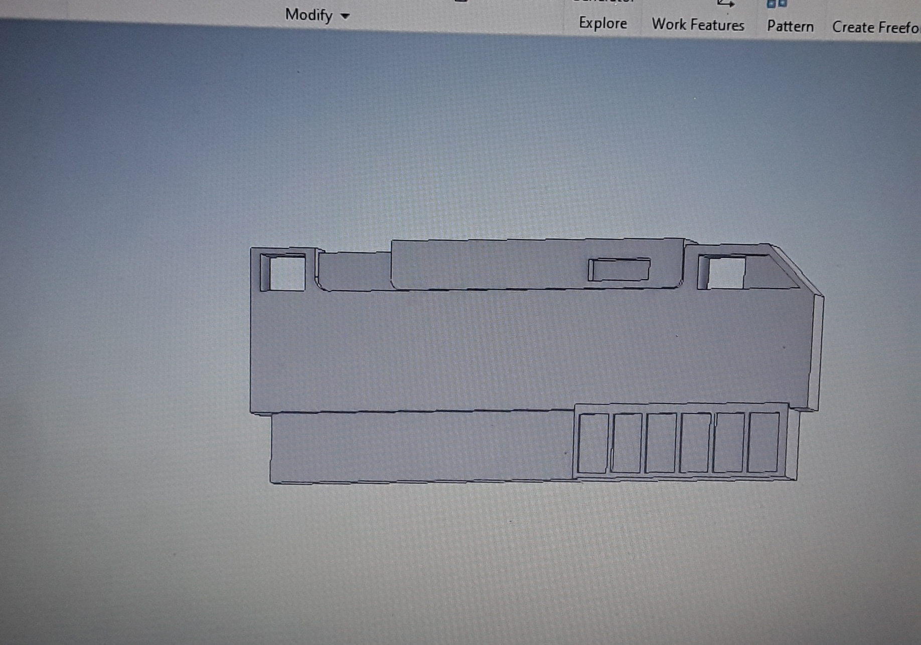
Project_Journey_Files/20220815_222312.jpg
