C-Falconer/Inscryption/Project_Journey_Files/20220815_222330.jpg

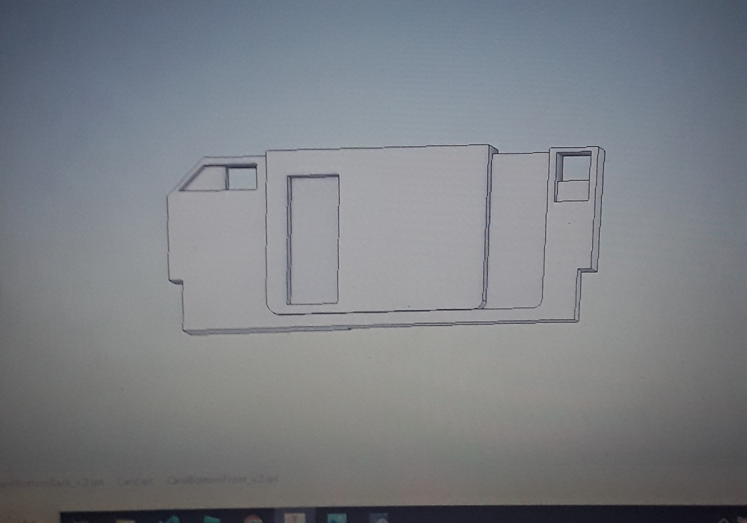
Project_Journey_Files/20220815_222330.jpg
