C-Falconer/Inscryption/Project_Journey_Files/20220818_055711.jpg

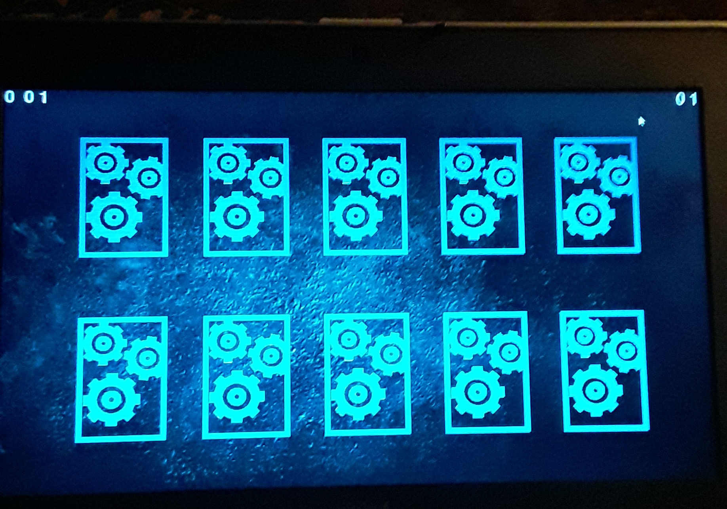
Project_Journey_Files/20220818_055711.jpg
