C-Falconer/Inscryption/Project_Journey_Files/20220924_013631.jpg

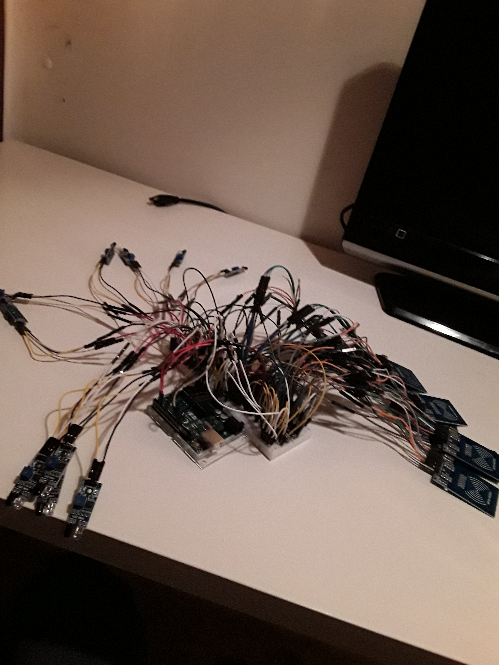
Project_Journey_Files/20220924_013631.jpg
