C-Falconer/Inscryption/Code/Python/Resources/Images/Cards/Busted_Printer.png

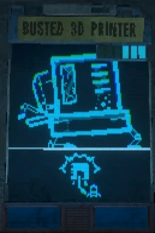
Code/Python/Resources/Images/Cards/Busted_Printer.png
